ElektorLabs/J2B-Synthesizer/Firmware/J2B_synthesizer_3.0/src/waveforms_delayertron.c

/*
 * Waveforms_delayertron.h
 *
 * Created: 18/04/2014 22:35:02
 *  Author: Paul Soulsby
 */ 


#include "atmegatron.h"

#if PRODUCT==DELAYERTRON

const sample_t wave_store[2][16][WAVE_LEN] = {
{
	{0,127,127,127,127,127,127,127,127,127,127,127,127,127,127,127,127,127,127,127,127,127,127,127,127,127,127,127,127,127,127,127,127,127,127,127,127,127,127,127,127,127,127,127,127,127,127,127,127,127,127,127,127,127,127,127,127,127,127,127,127,127,127,127,127,127,127,127,127,127,127,127,127,127,127,127,127,127,127,127,127,127,127,127,127,127,127,127,127,127,127,127,127,127,127,127,127,127,127,127,127,127,127,127,127,127,127,127,127,127,127,127,127,127,127,127,127,127,127,127,127,127,127,127,127,127,127,127,0,-127,-127,-127,-127,-127,-127,-127,-127,-127,-127,-127,-127,-127,-127,-127,-127,-127,-127,-127,-127,-127,-127,-127,-127,-127,-127,-127,-127,-127,-127,-127,-127,-127,-127,-127,-127,-127,-127,-127,-127,-127,-127,-127,-127,-127,-127,-127,-127,-127,-127,-127,-127,-127,-127,-127,-127,-127,-127,-127,-127,-127,-127,-127,-127,-127,-127,-127,-127,-127,-127,-127,-127,-127,-127,-127,-127,-127,-127,-127,-127,-127,-127,-127,-127,-127,-127,-127,-127,-127,-127,-127,-127,-127,-127,-127,-127,-127,-127,-127,-127,-127,-127,-127,-127,-127,-127,-127,-127,-127,-127,-127,-127,-127,-127,-127,-127,-127,-127,-127,-127,-127,-127,-127,-127,-127,-127,-127}, //square
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
		//{9,9,9,9,9,9,9,9,9,9,9,58,58,58,58,9,9,9,9,9,9,9,9,9,9,9,9,9,9,9,9,9,9,9,9,9,9,9,9,127,127,127,127,127,127,127,127,127,127,127,127,127,127,127,127,127,127,15,15,15,15,15,15,15,15,15,15,15,15,15,15,8,-40,8,8,8,8,8,8,8,8,8,8,8,8,8,8,8,8,8,8,-39,-39,-39,-39,8,8,8,8,8,8,8,8,8,8,8,57,57,57,57,8,8,8,8,8,8,8,8,8,8,8,8,8,8,8,8,8,8,8,8,8,8,8,8,-88,-49,-57,-46,8,8,8,8,8,8,8,8,8,8,8,8,8,8,8,8,8,8,8,8,8,-39,-39,-39,8,8,8,8,8,8,8,8,8,8,8,54,57,57,55,8,8,8,8,8,8,8,8,8,8,8,8,8,8,8,8,8,8,8,8,8,-122,-122,-122,-122,-122,-122,-122,-122,-122,-122,-122,-122,-122,-122,-122,-122,-122,-122,-122,-122,-122,-122,-122,-122,-122,-122,-122,-121,-121,-121,-121,9,9,9,9,9,9,9,9,9,9,9,9,9,9,9,9,9,9,9,9,9,9,9,9,-38,-38,-38},  //chip 2
//
//
	//}
//};
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
