ElektorLabs/J2B-Synthesizer/Firmware/J2B_synthesizer_3.0/src/wavestore.c

/*
Copyright 2014 Paul Soulsby www.soulsbysynths.com
    This file is part of Atmegatron.

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
    You should have received a copy of the GNU General Public License
    along with Atmegadrum.  If not, see <http://www.gnu.org/licenses/>.
*/

#include "atmegatron.h"


#if PRODUCT==ATMEGADRUM

#define WAVESTORE_SIZE  19249

const sample_t wave_store[WAVESTORE_SIZE] =
{
  //kick1.wav
  0,-4,4,-4,63,20,-47,-16,-32,-84,-55,12,70,83,34,36,-16,-35,-52,-95,10,14,-2,6,10,28,50,44,21,24,47,56,
  38,17,21,-10,-52,-82,-84,-90,-55,-80,-94,-67,-9,-50,-11,42,40,31,23,63,50,52,41,58,27,8,-7,34,32,44,39,65,
  45,36,16,27,8,1,-18,-21,-15,-5,-5,-49,-90,-107,-113,-114,-100,-98,-77,-57,-25,-6,44,32,38,25,31,24,27,20,10,4,
  4,29,44,59,61,66,67,59,38,47,36,-3,-8,0,-7,-22,-13,-19,-12,9,0,13,19,9,15,19,23,23,13,1,16,0,
  -27,-29,-39,-44,-36,-51,-42,-31,-36,-48,-31,-36,-25,-13,-34,-36,-11,-14,-44,-35,-31,-14,-19,-20,-21,-9,0,24,25,19,21,23,
  23,17,13,16,22,28,18,12,10,0,3,20,39,15,24,43,43,30,40,48,37,47,56,59,65,60,52,32,11,20,17,18,
  -1,-25,-47,-54,-52,-67,-64,-75,-74,-64,-63,-51,-60,-49,-49,-45,-42,-35,-21,-8,2,14,18,24,24,33,40,46,57,61,56,62,
  68,60,51,45,41,29,13,14,5,-12,-31,-45,-51,-64,-80,-89,-96,-91,-87,-89,-88,-91,-80,-76,-77,-76,-71,-63,-50,-43,-35,-19,
  -16,1,11,18,30,40,54,68,72,87,88,101,105,110,119,123,118,111,103,96,95,96,81,77,76,61,44,41,32,15,14,0,
  -8,-22,-27,-39,-41,-47,-55,-63,-67,-76,-84,-85,-89,-95,-96,-87,-78,-77,-68,-61,-48,-40,-36,-28,-34,-29,-25,-24,-18,-20,-11,4,
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
	}
};

#endif /* PRODUCT */


#if PRODUCT==ATMEGADRUM

const uint16_t wave_start[17] =
{
  0,1639,3330,5126,6513,8847,9767,10325,11004,12019,14250,14634,15063,15786,17680,18785,19249
};

inline sample_t Wavestore_Get_Sample(uint16_t index)
{
  return wave_store[index];
}

inline uint16_t Wavestore_Get_Start(byte index)
{
  return wave_start[index];
}

#endif /* PRODUCT */
