ElektorLabs/J2B-Synthesizer/Firmware/J2B_synthesizer_3.0/inc/eeprom.h

#ifndef __EEPROM_H__
#define __EEPROM_H__


// TODO: replace this structure by external EEPROM chip driver.
typedef struct
{
	void (*write)(uint32_t address, uint8_t value);
	uint8_t (*read)(uint32_t address);
}
eeprom_t;

extern eeprom_t EEPROM;


#endif // __EEPROM_H__
