ElektorLabs/J2B-Synthesizer/Firmware/J2B_synthesizer_3.0/libeeprom-v1_0/libeeprom.h

#ifndef API_H_
#define API_H_

#include <stdint.h>


/* Define IAP command codes */
enum {
    EELIB_IAP_COMMAND_EEPROM_WRITE = 61,
    EELIB_IAP_COMMAND_EEPROM_READ = 62,
};
    

/* Define IAP status codes */
enum {
    EELIB_IAP_STATUS_CMD_SUCCESS = 0,
    EELIB_IAP_STATUS_INVALID_COMMAND = 1,
    EELIB_IAP_STATUS_SRC_ADDR_ERROR = 2,
    EELIB_IAP_STATUS_DST_ADDR_ERROR = 3,
    EELIB_IAP_STATUS_SRC_ADDR_NOT_MAPPED = 4,
    EELIB_IAP_STATUS_DST_ADDR_NOT_MAPPED = 5,
    EELIB_IAP_STATUS_COUNT_ERROR = 6,
};
    
typedef uint32_t EELIB_Command[5];
typedef uint32_t EELIB_Result[5];

/* Entry point to libeeprom (replaces ROM IAP entry) */
void EELIB_entry (EELIB_Command command, EELIB_Result result);

/* Return version number */
uint32_t EELIB_getVersion (void);

#endif  /* ifndef API_H_ */
